PaulaFont/Uno-Mate/miscelanea/Disseny_a_ma_2.jpeg

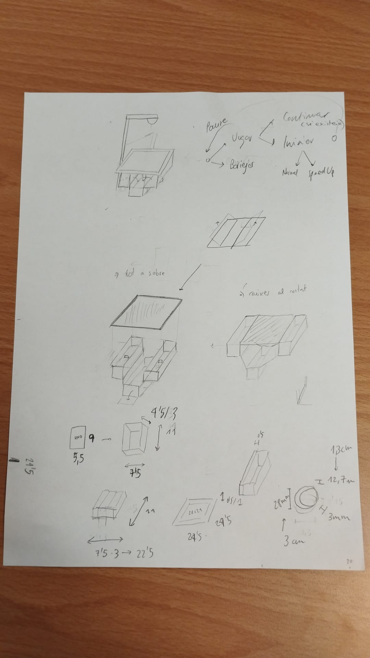
miscelanea/Disseny_a_ma_2.jpeg
