PaulaFont/Uno-Mate/src/Raspberry_pi_code/frame1.jpg

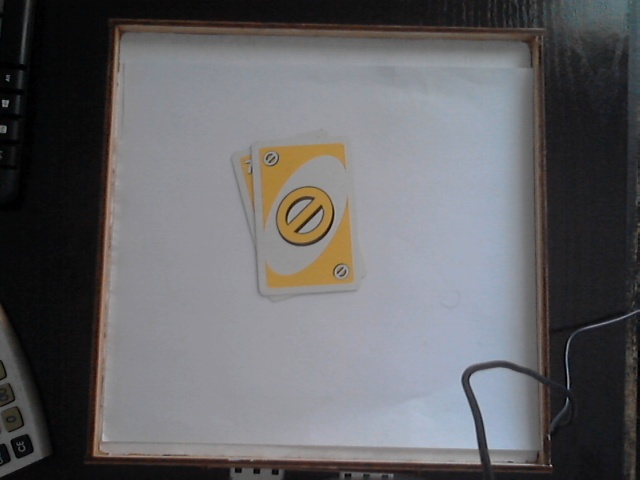
src/Raspberry_pi_code/frame1.jpg
