PaulaFont/Uno-Mate/src/Raspberry_pi_code/imatge_final.jpg

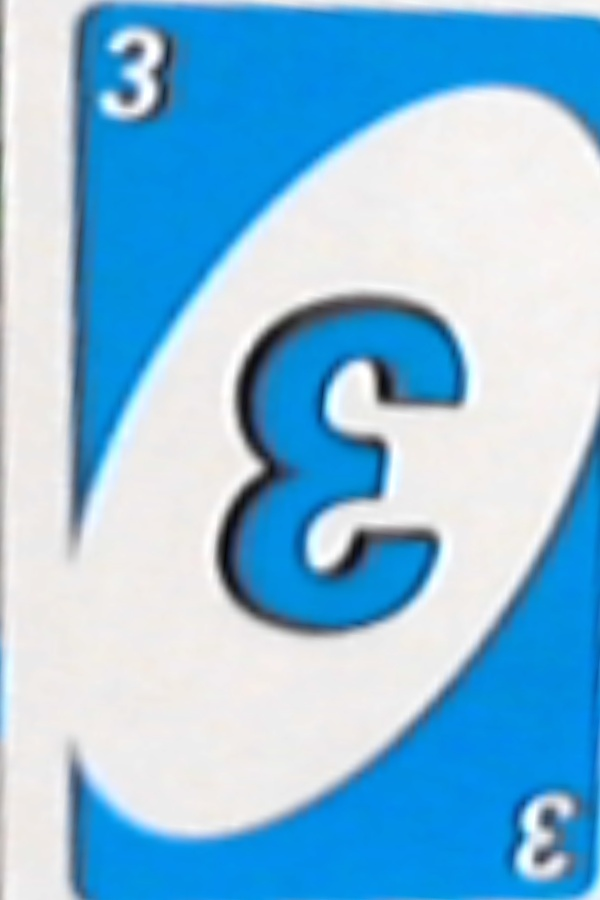
src/Raspberry_pi_code/imatge_final.jpg
