PaulaFont/Uno-Mate/src/Raspberry_pi_code/Imatge_inicial.jpg

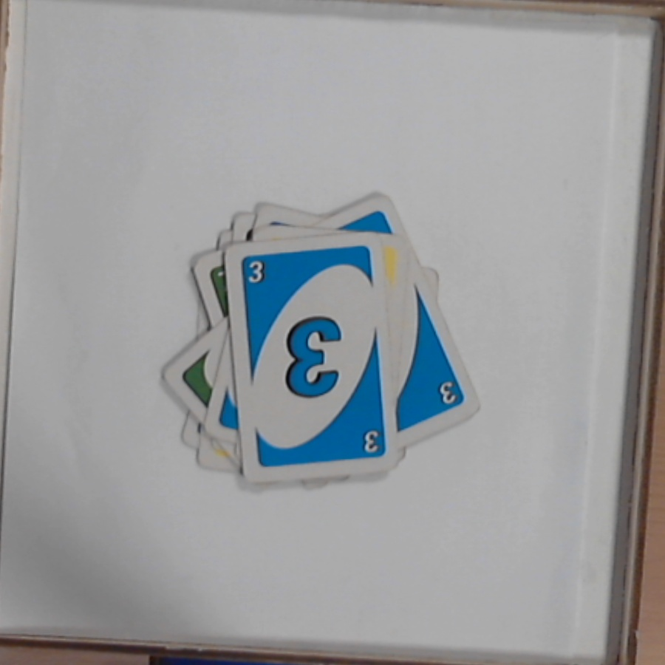
src/Raspberry_pi_code/Imatge_inicial.jpg
