PaulaFont/Uno-Mate/src/Raspberry_pi_code/prova_partida_entrega/WIN_20240517_11_30_35_Pro.jpg

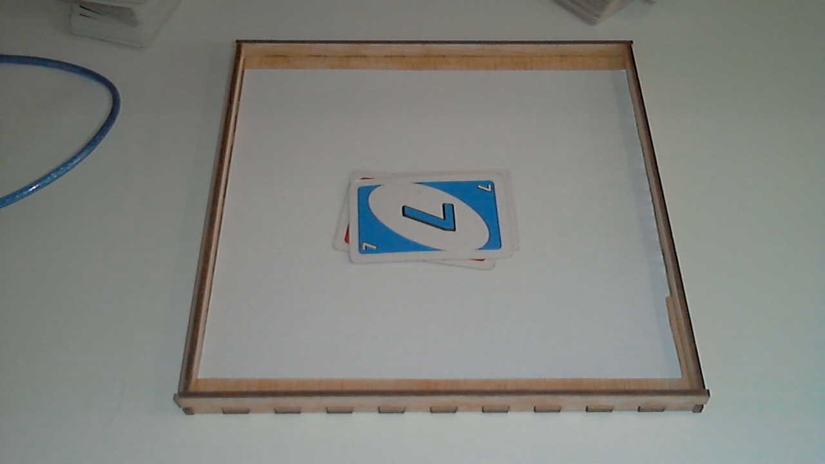
src/Raspberry_pi_code/prova_partida_entrega/WIN_20240517_11_30_35_Pro.jpg
