PaulaFont/Uno-Mate/src/Raspberry_pi_code/prova_partida_entrega/WIN_20240517_11_35_45_Pro.jpg

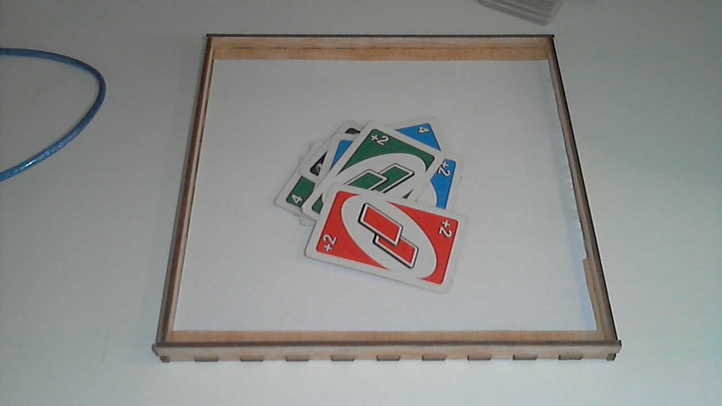
src/Raspberry_pi_code/prova_partida_entrega/WIN_20240517_11_35_45_Pro.jpg
