PaulaFont/Uno-Mate/src/Raspberry_pi_code/video_partida/frame.jpg

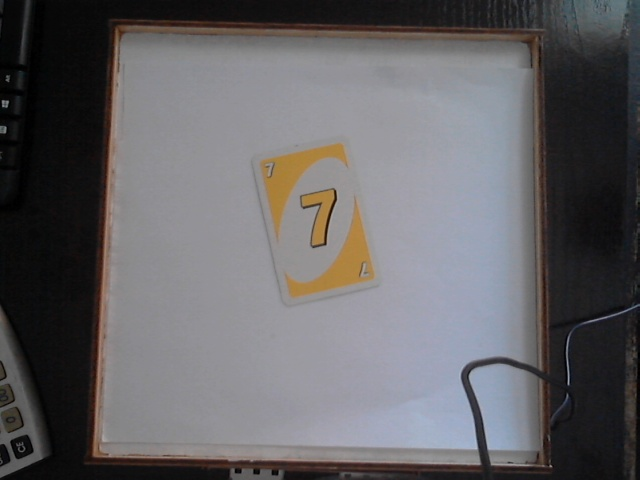
src/Raspberry_pi_code/video_partida/frame.jpg
