PaulaFont/Uno-Mate/src/Raspberry_pi_code/WIN_20240529_17_58_48_Pro.jpg

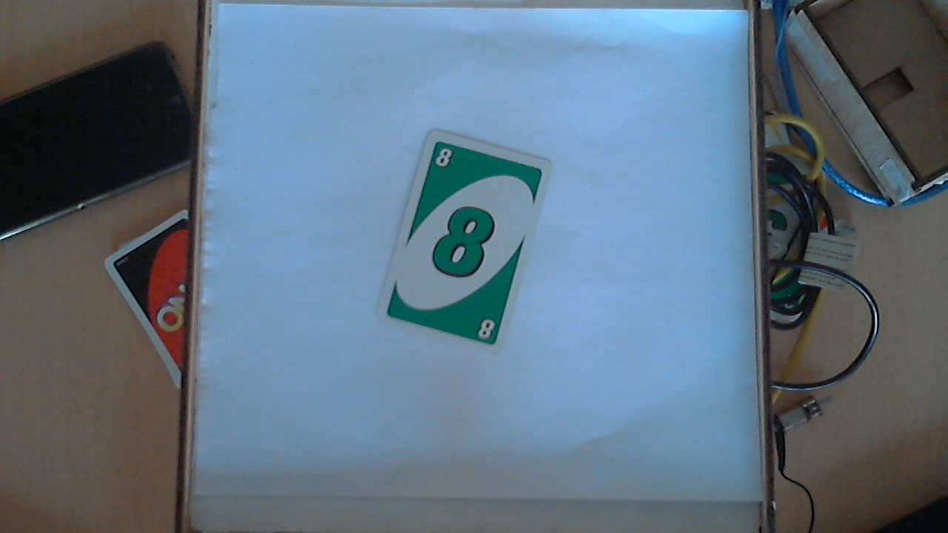
src/Raspberry_pi_code/WIN_20240529_17_58_48_Pro.jpg
